mora200217/walle-cubesat-kit/walle_sensors/sensor.py

from abc import ABC, abstractmethod

class Sensor(ABC): 
    def __init__(self): 
        self.units = "mm"
        self.available = False

    @abstractmethod
    def setup(self) -> bool: 
        print("Please implement setup setting")
        return True 

    @abstractmethod
    def read(self): 
        print("Please implement read setting")
        pass 



        
